haum/GHaumCube64/structure/placement/Doc_fabrication/Centre_Support-Dessus.dxf

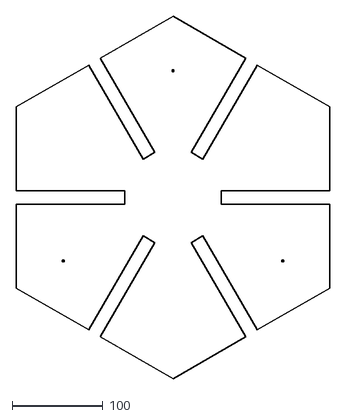
[picture p18: CAD file, 2021-09-17]
structure/placement/Doc_fabrication/Centre_Support-Dessus.dxf
346.4 x 400.0
