haum/GHaumCube64/structure/placement/Doc_fabrication/Centre_Support.FCStd

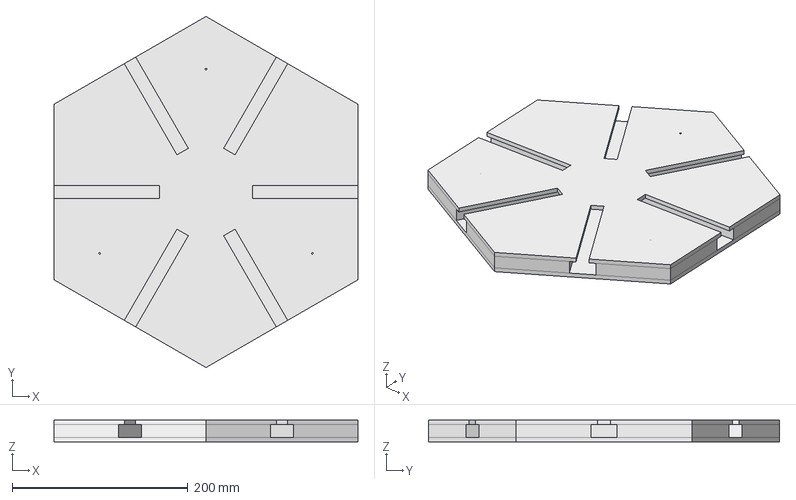
[picture p19: CAD file, 2021-09-17]
structure/placement/Doc_fabrication/Centre_Support.FCStd
346.4 x 400.0 x 25.0 mm
