haum/GHaumCube64/structure/placement/Doc_fabrication/Centre_Support-Dessous.dxf

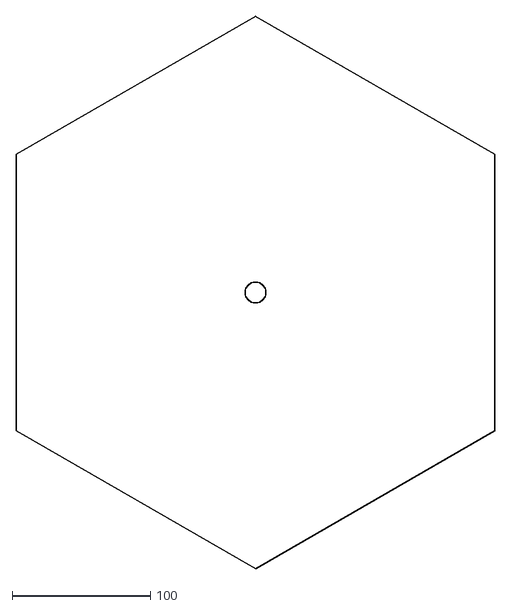
[picture p20: CAD file, 2021-09-17]
structure/placement/Doc_fabrication/Centre_Support-Dessous.dxf
346.4 x 400.0
